ILikeNickelback/OpenJTS/docs/software/api/workers.rst

workers
=======

.. automodule:: workers

.. rubric:: Modules

.. autosummary::
   :toctree:
   :recursive:

   base_worker
   calibration_worker
   frequency_worker
   sequence_worker
