ILikeNickelback/OpenJTS/software/src/hardware/adc_frequency.py

"""ADC driver subclass for frequency-domain experiments.

The board simultaneously generates a stimulus waveform (sinusoidal actinic
light + detection pulses, built by :class:`FrequencyWaveformBuilder`) on its
AO/digital outputs and captures the photodiode response on its AI inputs using
a retriggered background scan.
"""

import numpy as np
from mcculw import ul
from mcculw.enums import (
    DigitalIODirection,
)

from config.config import config

from sequence_builders.frequency_waveform_builder import FrequencyWaveformBuilder
from hardware.adc_base import ADCBase


class FrequencyAcquisitionADC(ADCBase):
    """ADC driver for frequency-domain experiments.

    Generates a multi-channel stimulus waveform (sinusoidal actinic light plus
    detection pulses) on the board's AO/digital outputs while simultaneously
    capturing the photodiode response on the AI inputs via a retriggered
    background scan.

    Typical call order::

        adc = FrequencyAcquisitionADC()
        n_pulses = adc.configure(frequency_config)  # build waveform, allocate buffers
        adc.start_reader()                           # start background reader thread
        adc.start_acquisition()                      # start AI + AO/digital scans
        # ... consume blocks via adc.read_block() ...
        adc.stop_acquisition()                       # stop all scans, free buffers
        adc.reset_actinic_light()                    # zero AO outputs

    Attributes:
        rate (float): Analog output sample rate in Hz, from ``config["ADC"]["output_rate"]``.
        pulse_times_ms (list[float]): Timestamps (ms) of each detection pulse in the
            waveform; populated by :meth:`configure`.
    """

    def __init__(self):
        """Initialise the waveform builder and internal sample counters."""
        super().__init__()
        self.rate: float = config["ADC"]["output_rate"]
        self._total_waveform_samples: int = 0
        self._total_acq_samples: int = 0
        self._waveform_builder = FrequencyWaveformBuilder(self.board_num, self.rate)
        self.pulse_times_ms: list[float] = []

    def configure(self, frequency_config: dict) -> int:
        """Build the stimulus waveform, allocate buffers, and arm the AI scan.

        Configures all digital ports as outputs, builds an interleaved
        AO+digital waveform, copies it into the 16-bit buffer, allocates
        the 32-bit acquisition buffer, and writes the trigger count register.

        Args:
            frequency_config: Frequency experiment parameters dict (from config
                or the UI), passed directly to :class:`FrequencyWaveformBuilder`.

        Returns:
            Number of detection pulses in the waveform.  The worker uses this
            to know how many trigger blocks to expect.
        """
        for port in self.dev_info.get_dio_info().port_info:
            if port.is_port_configurable:
                ul.d_config_port(self.board_num, port.type, DigitalIODirection.OUT)

        interleaved, self._total_waveform_samples, number_of_pulses = (
            self._waveform_builder.build(frequency_config)
        )

        # Activate this line to debug waveform generation
        # self._waveform_builder.plot(frequency_config)
        self.pulse_times_ms = self._waveform_builder.pulse_times_ms

        self.nbr_of_triggers_per_sample = 1 + config["Sampling"].get(
            "number_of_points_before_flash", 1
        )
        self._total_acq_samples = (
            number_of_pulses
            * self.samples_per_trigger
            * self.nbr_of_triggers_per_sample
        )

        self._alloc_waveform_buffer_16(len(interleaved))
        if self._c_waveform_array is not None:
            arr_view = np.ctypeslib.as_array(
                self._c_waveform_array, shape=(len(interleaved),)
            )
            arr_view[:] = interleaved

        self._alloc_acq_buffer_32(self._total_acq_samples)
        self._configure_trigger_count()

        return number_of_pulses
